meerstern/ToF_UVC_Cam/firm/UVC_RP2040/tmf8829_image.c

/**************************************************************************************************
* Copyright � 2024 ams-OSRAM AG                                                                   *
* All rights are reserved.                                                                        *
*                                                                                                 *
* FOR FULL LICENSE TEXT SEE LICENSES-MIT.TXT                                                      *
*                                                                                                 *
**************************************************************************************************/

#include "tmf8829_shim.h"
#include "tmf8829_image.h"

/* http://srecord.sourceforge.net/ */
const unsigned char tmf8829_image[] =
{
0x00, 0xC0, 0x01, 0x00, 0xC1, 0x00, 0x01, 0x00, 0xED, 0x12, 0x00, 0x00,
0xF1, 0x12, 0x00, 0x00, 0xF5, 0x12, 0x00, 0x00, 0xF9, 0x12, 0x00, 0x00,
0xFD, 0x12, 0x00, 0x00, 0x01, 0x13, 0x00, 0x00, 0x05, 0x13, 0x00, 0x00,
0x00, 0x00, 0x00, 0x00, 0x00, 0x00, 0x00, 0x00, 0x09, 0x13, 0x00, 0x00,
0x0D, 0x13, 0x00, 0x00, 0x00, 0x00, 0x00, 0x00, 0x11, 0x13, 0x00, 0x00,
0x15, 0x13, 0x00, 0x00, 0xEB, 0x12, 0x00, 0x00, 0xEB, 0x12, 0x00, 0x00,
0x85, 0x02, 0x01, 0x00, 0x21, 0x02, 0x01, 0x00, 0x75, 0x01, 0x01, 0x00,
0x69, 0x14, 0x00, 0x00, 0xEB, 0x12, 0x00, 0x00, 0xAD, 0x14, 0x00, 0x00,
0x55, 0x01, 0x01, 0x00, 0xEB, 0x12, 0x00, 0x00, 0x0D, 0x15, 0x00, 0x00,
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
const unsigned long tmf8829_image_length      = 0x000036D0;

#define TMF8829_IMAGE_TERMINATION 0x000100C1
#define TMF8829_IMAGE_START       0x00010000
#define TMF8829_IMAGE_FINISH      0x000136D0
#define TMF8829_IMAGE_LENGTH      0x000036D0
