meerstern/ToF_UVC_Cam/firm/UVC_RP2040/tmf8829_app.h

/**************************************************************************************************
* Copyright © 2024 ams-OSRAM AG                                                                   *
* All rights are reserved.                                                                        *
*                                                                                                 *
* FOR FULL LICENSE TEXT SEE LICENSES-MIT.TXT                                                      *
*                                                                                                 *
**************************************************************************************************/

/** @file This is the tmf8829 arduino uno driver example console application. 
 */

#ifndef TMF8829_APP_H
#define TMF8829_APP_H

// ---------------------------------------------- includes ----------------------------------------
#include "tmf8829_shim.h"
// ---------------------------------------------- functions ---------------------------------------

/** @brief Arduino setup function is only called once at startup. Do all the HW initialisation stuff here.
 * @param logLevelIdx ...  the log level index to be used (0..8 -> see logLevels array in tmf8829_app.cpp)
 * @param  baudrate ... for the serial input the baudrate
 * @param  i2cClockSpeedInHz ... the i2c frequency
 */
void setupFn( uint8_t logLevelIdx, uint32_t baudrate, uint32_t i2cClockSpeedInHz );

/** @brief Arduino main loop function, is executed cyclic
 * @return 1 if wants to be called again
 * @return 0 if program should terminate
 */
int8_t loopFn( );

/** @brief Arduino terminate function is only called once when exit key 'q' is pressed. Write a message and wait for shutdown of arduino.
 */
void terminateFn( );

void measure ( );
void enable ( uint32_t imageStartAddress, const unsigned char * image, int32_t imageSizeInBytes );
void preconfigure ( int8_t cfgNr );

#endif // TMF8829_APP_H
