meerstern/ToF_UVC_Cam/firm/UVC_RP2040/tmf8829_image.h

/**************************************************************************************************
* Copyright © 2024 ams-OSRAM AG                                                                   *
* All rights are reserved.                                                                        *
*                                                                                                 *
* FOR FULL LICENSE TEXT SEE LICENSES-MIT.TXT                                                      *
*                                                                                                 *
**************************************************************************************************/

#ifndef TMF8829_IMAGE_H
#define TMF8829_IMAGE_H

extern const unsigned long tmf8829_image_termination;
extern const unsigned long tmf8829_image_start;
extern const unsigned long tmf8829_image_finish;
extern const unsigned long tmf8829_image_length;
extern const unsigned char tmf8829_image[];

#endif /* TMF8829_IMAGE_H */
